cyrilknops/intelliflow/2020-2021/PCB/TestCodesPCB/UART_Master/UART_Master.ino

const char *sending = "Hello from ESP32";
String reading;
  
void setup()
{
  Serial.begin(115200);
}
void loop()
{
  Serial.println(sending);             
 
   while(Serial.available()) 
   {
   reading = Serial.readString();// read the incoming data as string  
   Serial.println(reading);// string is recieved but it will send it back to the psoc4
   }
   
  delay(1000);
}
