cyrilknops/intelliflow/2020-2021/PCB/TestCodesPCB/PSoc_Slave_Codes/SPI_Slave_FullDuplex.cydsn/codegentemp/UART_Putty_BOOT.h

/***************************************************************************//**
* \file UART_Putty_BOOT.h
* \version 4.0
*
* \brief
*  This file provides constants and parameter values of the bootloader
*  communication APIs for the SCB Component.
*
* Note:
*
********************************************************************************
* \copyright
* Copyright 2014-2017, Cypress Semiconductor Corporation. All rights reserved.
* You may use this file only in accordance with the license, terms, conditions,
* disclaimers, and limitations in the end user license agreement accompanying
* the software package with which this file was provided.
*******************************************************************************/

#if !defined(CY_SCB_BOOT_UART_Putty_H)
#define CY_SCB_BOOT_UART_Putty_H

#include "UART_Putty_PVT.h"

#if (UART_Putty_SCB_MODE_I2C_INC)
    #include "UART_Putty_I2C.h"
#endif /* (UART_Putty_SCB_MODE_I2C_INC) */

#if (UART_Putty_SCB_MODE_EZI2C_INC)
    #include "UART_Putty_EZI2C.h"
#endif /* (UART_Putty_SCB_MODE_EZI2C_INC) */

#if (UART_Putty_SCB_MODE_SPI_INC || UART_Putty_SCB_MODE_UART_INC)
    #include "UART_Putty_SPI_UART.h"
#endif /* (UART_Putty_SCB_MODE_SPI_INC || UART_Putty_SCB_MODE_UART_INC) */


/***************************************
*  Conditional Compilation Parameters
****************************************/

/* Bootloader communication interface enable */
#define UART_Putty_BTLDR_COMM_ENABLED ((CYDEV_BOOTLOADER_IO_COMP == CyBtldr_UART_Putty) || \
                                             (CYDEV_BOOTLOADER_IO_COMP == CyBtldr_Custom_Interface))

/* Enable I2C bootloader communication */
#if (UART_Putty_SCB_MODE_I2C_INC)
    #define UART_Putty_I2C_BTLDR_COMM_ENABLED     (UART_Putty_BTLDR_COMM_ENABLED && \
                                                            (UART_Putty_SCB_MODE_UNCONFIG_CONST_CFG || \
                                                             UART_Putty_I2C_SLAVE_CONST))
#else
     #define UART_Putty_I2C_BTLDR_COMM_ENABLED    (0u)
#endif /* (UART_Putty_SCB_MODE_I2C_INC) */

/* EZI2C does not support bootloader communication. Provide empty APIs */
#if (UART_Putty_SCB_MODE_EZI2C_INC)
    #define UART_Putty_EZI2C_BTLDR_COMM_ENABLED   (UART_Putty_BTLDR_COMM_ENABLED && \
                                                         UART_Putty_SCB_MODE_UNCONFIG_CONST_CFG)
#else
    #define UART_Putty_EZI2C_BTLDR_COMM_ENABLED   (0u)
#endif /* (UART_Putty_EZI2C_BTLDR_COMM_ENABLED) */

/* Enable SPI bootloader communication */
#if (UART_Putty_SCB_MODE_SPI_INC)
    #define UART_Putty_SPI_BTLDR_COMM_ENABLED     (UART_Putty_BTLDR_COMM_ENABLED && \
                                                            (UART_Putty_SCB_MODE_UNCONFIG_CONST_CFG || \
                                                             UART_Putty_SPI_SLAVE_CONST))
#else
        #define UART_Putty_SPI_BTLDR_COMM_ENABLED (0u)
#endif /* (UART_Putty_SPI_BTLDR_COMM_ENABLED) */

/* Enable UART bootloader communication */
#if (UART_Putty_SCB_MODE_UART_INC)
       #define UART_Putty_UART_BTLDR_COMM_ENABLED    (UART_Putty_BTLDR_COMM_ENABLED && \
                                                            (UART_Putty_SCB_MODE_UNCONFIG_CONST_CFG || \
                                                             (UART_Putty_UART_RX_DIRECTION && \
                                                              UART_Putty_UART_TX_DIRECTION)))
#else
     #define UART_Putty_UART_BTLDR_COMM_ENABLED   (0u)
#endif /* (UART_Putty_UART_BTLDR_COMM_ENABLED) */

/* Enable bootloader communication */
#define UART_Putty_BTLDR_COMM_MODE_ENABLED    (UART_Putty_I2C_BTLDR_COMM_ENABLED   || \
                                                     UART_Putty_SPI_BTLDR_COMM_ENABLED   || \
                                                     UART_Putty_EZI2C_BTLDR_COMM_ENABLED || \
                                                     UART_Putty_UART_BTLDR_COMM_ENABLED)


/***************************************
*        Function Prototypes
***************************************/

#if defined(CYDEV_BOOTLOADER_IO_COMP) && (UART_Putty_I2C_BTLDR_COMM_ENABLED)
    /* I2C Bootloader physical layer functions */
    void UART_Putty_I2CCyBtldrCommStart(void);
    void UART_Putty_I2CCyBtldrCommStop (void);
    void UART_Putty_I2CCyBtldrCommReset(void);
    cystatus UART_Putty_I2CCyBtldrCommRead       (uint8 pData[], uint16 size, uint16 * count, uint8 timeOut);
    cystatus UART_Putty_I2CCyBtldrCommWrite(const uint8 pData[], uint16 size, uint16 * count, uint8 timeOut);

    /* Map I2C specific bootloader communication APIs to SCB specific APIs */
    #if (UART_Putty_SCB_MODE_I2C_CONST_CFG)
        #define UART_Putty_CyBtldrCommStart   UART_Putty_I2CCyBtldrCommStart
        #define UART_Putty_CyBtldrCommStop    UART_Putty_I2CCyBtldrCommStop
        #define UART_Putty_CyBtldrCommReset   UART_Putty_I2CCyBtldrCommReset
        #define UART_Putty_CyBtldrCommRead    UART_Putty_I2CCyBtldrCommRead
        #define UART_Putty_CyBtldrCommWrite   UART_Putty_I2CCyBtldrCommWrite
    #endif /* (UART_Putty_SCB_MODE_I2C_CONST_CFG) */

#endif /* defined(CYDEV_BOOTLOADER_IO_COMP) && (UART_Putty_I2C_BTLDR_COMM_ENABLED) */


#if defined(CYDEV_BOOTLOADER_IO_COMP) && (UART_Putty_EZI2C_BTLDR_COMM_ENABLED)
    /* Bootloader physical layer functions */
    void UART_Putty_EzI2CCyBtldrCommStart(void);
    void UART_Putty_EzI2CCyBtldrCommStop (void);
    void UART_Putty_EzI2CCyBtldrCommReset(void);
    cystatus UART_Putty_EzI2CCyBtldrCommRead       (uint8 pData[], uint16 size, uint16 * count, uint8 timeOut);
    cystatus UART_Putty_EzI2CCyBtldrCommWrite(const uint8 pData[], uint16 size, uint16 * count, uint8 timeOut);

    /* Map EZI2C specific bootloader communication APIs to SCB specific APIs */
    #if (UART_Putty_SCB_MODE_EZI2C_CONST_CFG)
        #define UART_Putty_CyBtldrCommStart   UART_Putty_EzI2CCyBtldrCommStart
        #define UART_Putty_CyBtldrCommStop    UART_Putty_EzI2CCyBtldrCommStop
        #define UART_Putty_CyBtldrCommReset   UART_Putty_EzI2CCyBtldrCommReset
        #define UART_Putty_CyBtldrCommRead    UART_Putty_EzI2CCyBtldrCommRead
        #define UART_Putty_CyBtldrCommWrite   UART_Putty_EzI2CCyBtldrCommWrite
    #endif /* (UART_Putty_SCB_MODE_EZI2C_CONST_CFG) */

#endif /* defined(CYDEV_BOOTLOADER_IO_COMP) && (UART_Putty_EZI2C_BTLDR_COMM_ENABLED) */

#if defined(CYDEV_BOOTLOADER_IO_COMP) && (UART_Putty_SPI_BTLDR_COMM_ENABLED)
    /* SPI Bootloader physical layer functions */
    void UART_Putty_SpiCyBtldrCommStart(void);
    void UART_Putty_SpiCyBtldrCommStop (void);
    void UART_Putty_SpiCyBtldrCommReset(void);
    cystatus UART_Putty_SpiCyBtldrCommRead       (uint8 pData[], uint16 size, uint16 * count, uint8 timeOut);
    cystatus UART_Putty_SpiCyBtldrCommWrite(const uint8 pData[], uint16 size, uint16 * count, uint8 timeOut);

    /* Map SPI specific bootloader communication APIs to SCB specific APIs */
    #if (UART_Putty_SCB_MODE_SPI_CONST_CFG)
        #define UART_Putty_CyBtldrCommStart   UART_Putty_SpiCyBtldrCommStart
        #define UART_Putty_CyBtldrCommStop    UART_Putty_SpiCyBtldrCommStop
        #define UART_Putty_CyBtldrCommReset   UART_Putty_SpiCyBtldrCommReset
        #define UART_Putty_CyBtldrCommRead    UART_Putty_SpiCyBtldrCommRead
        #define UART_Putty_CyBtldrCommWrite   UART_Putty_SpiCyBtldrCommWrite
    #endif /* (UART_Putty_SCB_MODE_SPI_CONST_CFG) */

#endif /* defined(CYDEV_BOOTLOADER_IO_COMP) && (UART_Putty_SPI_BTLDR_COMM_ENABLED) */

#if defined(CYDEV_BOOTLOADER_IO_COMP) && (UART_Putty_UART_BTLDR_COMM_ENABLED)
    /* UART Bootloader physical layer functions */
    void UART_Putty_UartCyBtldrCommStart(void);
    void UART_Putty_UartCyBtldrCommStop (void);
    void UART_Putty_UartCyBtldrCommReset(void);
    cystatus UART_Putty_UartCyBtldrCommRead       (uint8 pData[], uint16 size, uint16 * count, uint8 timeOut);
    cystatus UART_Putty_UartCyBtldrCommWrite(const uint8 pData[], uint16 size, uint16 * count, uint8 timeOut);

    /* Map UART specific bootloader communication APIs to SCB specific APIs */
    #if (UART_Putty_SCB_MODE_UART_CONST_CFG)
        #define UART_Putty_CyBtldrCommStart   UART_Putty_UartCyBtldrCommStart
        #define UART_Putty_CyBtldrCommStop    UART_Putty_UartCyBtldrCommStop
        #define UART_Putty_CyBtldrCommReset   UART_Putty_UartCyBtldrCommReset
        #define UART_Putty_CyBtldrCommRead    UART_Putty_UartCyBtldrCommRead
        #define UART_Putty_CyBtldrCommWrite   UART_Putty_UartCyBtldrCommWrite
    #endif /* (UART_Putty_SCB_MODE_UART_CONST_CFG) */

#endif /* defined(CYDEV_BOOTLOADER_IO_COMP) && (UART_Putty_UART_BTLDR_COMM_ENABLED) */

/**
* \addtogroup group_bootloader
* @{
*/

#if defined(CYDEV_BOOTLOADER_IO_COMP) && (UART_Putty_BTLDR_COMM_ENABLED)
    #if (UART_Putty_SCB_MODE_UNCONFIG_CONST_CFG)
        /* Bootloader physical layer functions */
        void UART_Putty_CyBtldrCommStart(void);
        void UART_Putty_CyBtldrCommStop (void);
        void UART_Putty_CyBtldrCommReset(void);
        cystatus UART_Putty_CyBtldrCommRead       (uint8 pData[], uint16 size, uint16 * count, uint8 timeOut);
        cystatus UART_Putty_CyBtldrCommWrite(const uint8 pData[], uint16 size, uint16 * count, uint8 timeOut);
    #endif /* (UART_Putty_SCB_MODE_UNCONFIG_CONST_CFG) */

    /* Map SCB specific bootloader communication APIs to common APIs */
    #if (CYDEV_BOOTLOADER_IO_COMP == CyBtldr_UART_Putty)
        #define CyBtldrCommStart    UART_Putty_CyBtldrCommStart
        #define CyBtldrCommStop     UART_Putty_CyBtldrCommStop
        #define CyBtldrCommReset    UART_Putty_CyBtldrCommReset
        #define CyBtldrCommWrite    UART_Putty_CyBtldrCommWrite
        #define CyBtldrCommRead     UART_Putty_CyBtldrCommRead
    #endif /* (CYDEV_BOOTLOADER_IO_COMP == CyBtldr_UART_Putty) */

#endif /* defined(CYDEV_BOOTLOADER_IO_COMP) && (UART_Putty_BTLDR_COMM_ENABLED) */

/** @} group_bootloader */

/***************************************
*           API Constants
***************************************/

/* Timeout unit in milliseconds */
#define UART_Putty_WAIT_1_MS  (1u)

/* Return number of bytes to copy into bootloader buffer */
#define UART_Putty_BYTES_TO_COPY(actBufSize, bufSize) \
                            ( ((uint32)(actBufSize) < (uint32)(bufSize)) ? \
                                ((uint32) (actBufSize)) : ((uint32) (bufSize)) )

/* Size of Read/Write buffers for I2C bootloader  */
#define UART_Putty_I2C_BTLDR_SIZEOF_READ_BUFFER   (64u)
#define UART_Putty_I2C_BTLDR_SIZEOF_WRITE_BUFFER  (64u)

/* Byte to byte time interval: calculated basing on current component
* data rate configuration, can be defined in project if required.
*/
#ifndef UART_Putty_SPI_BYTE_TO_BYTE
    #define UART_Putty_SPI_BYTE_TO_BYTE   (160u)
#endif

/* Byte to byte time interval: calculated basing on current component
* baud rate configuration, can be defined in the project if required.
*/
#ifndef UART_Putty_UART_BYTE_TO_BYTE
    #define UART_Putty_UART_BYTE_TO_BYTE  (2086u)
#endif /* UART_Putty_UART_BYTE_TO_BYTE */

#endif /* (CY_SCB_BOOT_UART_Putty_H) */


/* [] END OF FILE */
