cyrilknops/intelliflow/2020-2021/PCB/TestCodesPCB/PSoc_Slave_Codes/I2C_slave.cydsn/codegentemp/EZI2C_EZI2C_INT.c

/***************************************************************************//**
* \file EZI2C_EZI2C_INT.c
* \version 4.0
*
* \brief
*  This file provides the source code to the Interrupt Service Routine for
*  the SCB Component in EZI2C mode.
*
* Note:
*
********************************************************************************
* \copyright
* Copyright 2013-2017, Cypress Semiconductor Corporation.  All rights reserved.
* You may use this file only in accordance with the license, terms, conditions,
* disclaimers, and limitations in the end user license agreement accompanying
* the software package with which this file was provided.
*******************************************************************************/

#include "EZI2C_PVT.h"
#include "EZI2C_EZI2C_PVT.h"
#include "cyapicallbacks.h"

#if(EZI2C_EZI2C_SCL_STRETCH_ENABLE_CONST)
    /*******************************************************************************
    * Function Name: EZI2C_EZI2C_STRETCH_ISR
    ****************************************************************************//**
    *
    *  Handles the Interrupt Service Routine for the SCB EZI2C mode.
    *  The clock stretching is used during operation.
    *
    *******************************************************************************/
    CY_ISR_PROTO(EZI2C_EZI2C_STRETCH_ISR)
    {
        static uint16 locBufSize;
        uint32 locIndex;
        uint32 locStatus;

        uint32 endTransfer;
        uint32 fifoIndex;
        uint32 locByte;

        uint32 locIntrCause;
        uint32 locIntrSlave;

    #ifdef EZI2C_EZI2C_STRETCH_ISR_ENTRY_CALLBACK
        EZI2C_EZI2C_STRETCH_ISR_EntryCallback();
    #endif /* EZI2C_EZI2C_STRETCH_ISR_ENTRY_CALLBACK */

    #if(EZI2C_SECONDARY_ADDRESS_ENABLE_CONST)
        /* Variable intended to be used with either buffer */
        static volatile uint8 * EZI2C_dataBuffer; /* Pointer to data buffer              */
        static uint16 EZI2C_bufSizeBuf;           /* Size of buffer in bytes             */
        static uint16 EZI2C_protectBuf;           /* Start index of write protected area */

        static uint8 activeAddress;
        uint32 ackResponse;

        ackResponse = EZI2C_EZI2C_ACK_RECEIVED_ADDRESS;
    #endif /* (EZI2C_SECONDARY_ADDRESS_ENABLE_CONST) */

    #if !defined (CY_REMOVE_EZI2C_CUSTOM_INTR_HANDLER)
        if(NULL != EZI2C_customIntrHandler)
        {
            EZI2C_customIntrHandler();
        }
    #else
        CY_EZI2C_CUSTOM_INTR_HANDLER();
    #endif /* !defined (CY_REMOVE_EZI2C_CUSTOM_INTR_HANDLER) */

        /* Make local copy of global variable */
        locIndex = EZI2C_EZI2C_GET_INDEX(activeAddress);

        /* Get interrupt sources */
        locIntrSlave = EZI2C_GetSlaveInterruptSource();
        locIntrCause = EZI2C_GetInterruptCause();

        /* INTR_SLAVE.I2C_ARB_LOST and INTR_SLAVE_I2C.BUS_ERROR */
        /* Handles errors on the bus. There are cases when both bits are set.
        * The error recovery is common: re-enable the scb IP. The content of the RX FIFO is lost.
        */
        if(0u != (locIntrSlave & (EZI2C_INTR_SLAVE_I2C_ARB_LOST |
                                  EZI2C_INTR_SLAVE_I2C_BUS_ERROR)))
        {
            EZI2C_CTRL_REG &= (uint32) ~EZI2C_CTRL_ENABLED; /* Disable SCB block */

        #if(EZI2C_CY_SCBIP_V0)
            if(0u != ((uint8) EZI2C_EZI2C_STATUS_BUSY & EZI2C_curStatus))
        #endif /* (EZI2C_CY_SCBIP_V0) */
            {
                EZI2C_curStatus &= (uint8) ~EZI2C_EZI2C_STATUS_BUSY;
                EZI2C_curStatus |= (uint8)  EZI2C_EZI2C_STATUS_ERR;

                /* INTR_TX_EMPTY is enabled in the address phase to receive data */
                if(0u == (EZI2C_GetTxInterruptMode() & EZI2C_INTR_TX_EMPTY))
                {
                    /* Write complete */
                    if(EZI2C_indexBuf1 != EZI2C_offsetBuf1)
                    {
                        EZI2C_curStatus |= (uint8) EZI2C_INTR_SLAVE_I2C_WRITE_STOP;
                    }
                }
                else
                {
                    /* Read complete */
                    EZI2C_curStatus |= (uint8) EZI2C_INTR_SLAVE_I2C_NACK;
                }
            }

            EZI2C_DISABLE_SLAVE_AUTO_DATA;

            /* Disable TX and RX interrupt sources */
            EZI2C_SetRxInterruptMode(EZI2C_NO_INTR_SOURCES);
            EZI2C_SetTxInterruptMode(EZI2C_NO_INTR_SOURCES);

        #if(EZI2C_CY_SCBIP_V0)
            /* Clear interrupt sources as they are not automatically cleared after SCB is disabled */
            EZI2C_ClearRxInterruptSource(EZI2C_INTR_RX_ALL);
            EZI2C_ClearSlaveInterruptSource(EZI2C_INTR_SLAVE_ALL);
        #endif /* (EZI2C_CY_SCBIP_V0) */

            EZI2C_fsmState = EZI2C_EZI2C_FSM_IDLE;

            EZI2C_CTRL_REG |= (uint32) EZI2C_CTRL_ENABLED;  /* Enable SCB block */
        }
        else
        {
            /* INTR_I2C_EC_WAKE_UP */
            /* Wakes up device from deep sleep */
            if(0u != (locIntrCause & EZI2C_INTR_CAUSE_I2C_EC))
            {
                /* Disables wakeup interrupt source but does not clear it. It is cleared in INTR_SLAVE_I2C_ADDR_MATCH */
                EZI2C_SetI2CExtClkInterruptMode(EZI2C_NO_INTR_SOURCES);
            }

            if(0u != (locIntrCause & (EZI2C_INTR_CAUSE_RX | EZI2C_INTR_CAUSE_SLAVE)))
            {
                /* INTR_RX.NOT_EMPTY */
                /* Receives data byte-by-byte. Does not use RX FIFO capabilities */
                if (0u != (EZI2C_GetRxInterruptSourceMasked() & EZI2C_INTR_RX_NOT_EMPTY))
                {
                #if(EZI2C_SECONDARY_ADDRESS_ENABLE_CONST)
                    /* If I2C_STOP service is delayed to I2C_ADDR_MATCH the address byte is in the RX FIFO and
                    * RX_NOT_EMPTY is enabled. The address byte has to stay into RX FIFO therefore
                    * RX.NOT_EMPTY service has to be skipped. The address byte has to be read by I2C_ADDR_MATCH.
                    */
                    if (0u == (locIntrCause & EZI2C_INTR_CAUSE_SLAVE))
                #endif /* (EZI2C_SECONDARY_ADDRESS_ENABLE_CONST) */
                    {
                        locByte = EZI2C_RX_FIFO_RD_REG;

                        switch(EZI2C_fsmState)
                        {
                        case EZI2C_EZI2C_FSM_BYTE_WRITE:
                            if(0u != locBufSize)
                            {
                                /* Store data byte and ACK */
                                EZI2C_I2C_SLAVE_GENERATE_ACK;

                                EZI2C_dataBuffer1[locIndex] = (uint8) locByte;
                                locIndex++;
                                locBufSize--;
                            }
                            else
                            {
                                /* Discard data byte and NACK */
                                EZI2C_I2C_SLAVE_GENERATE_NACK;
                            }
                            break;

                    #if(EZI2C_SUB_ADDRESS_SIZE16_CONST)
                        case EZI2C_EZI2C_FSM_OFFSET_HI8:

                            EZI2C_I2C_SLAVE_GENERATE_ACK;

                            /* Store offset most significant byre */
                            locBufSize = (uint16) ((uint8) locByte);

                            EZI2C_fsmState = EZI2C_EZI2C_FSM_OFFSET_LO8;

                            break;
                    #endif /* (EZI2C_SUB_ADDRESS_SIZE16_CONST) */

                        case EZI2C_EZI2C_FSM_OFFSET_LO8:

                            #if (EZI2C_SUB_ADDRESS_SIZE16)
                            {
                                /* Collect 2 bytes offset */
                                locByte = ((uint32) ((uint32) locBufSize << 8u)) | locByte;
                            }
                            #endif

                            /* Check offset against buffer size */
                            if(locByte < (uint32) EZI2C_bufSizeBuf1)
                            {
                                EZI2C_I2C_SLAVE_GENERATE_ACK;

                                /* Update local buffer index with new offset */
                                locIndex = locByte;

                                /* Get available buffer size to write */
                                locBufSize = (uint16) ((locByte < EZI2C_protectBuf1) ?
                                                       (EZI2C_protectBuf1 - locByte) : (0u));

                            #if(EZI2C_CY_SCBIP_V0)

                                if(locBufSize < EZI2C_EZI2C_FIFO_SIZE)
                                {
                                    /* Set FSM state to receive byte by byte */
                                    EZI2C_fsmState = EZI2C_EZI2C_FSM_BYTE_WRITE;
                                }
                                /* Receive RX FIFO chunks */
                                else if(locBufSize == EZI2C_EZI2C_FIFO_SIZE)
                                {
                                    EZI2C_ENABLE_SLAVE_AUTO_DATA; /* NACK when RX FIFO is full */
                                    EZI2C_SetRxInterruptMode(EZI2C_NO_INTR_SOURCES);
                                }
                                else
                                {
                                    EZI2C_ENABLE_SLAVE_AUTO_DATA_ACK; /* Stretch when RX FIFO is full */
                                    EZI2C_SetRxInterruptMode(EZI2C_INTR_RX_FULL);
                                }

                            #else

                                #if(EZI2C_SECONDARY_ADDRESS_ENABLE)
                                {
                                    /* Set FSM state to receive byte by byte.
                                    * The byte by byte receive is always chosen for two addresses. Ticket ID#175559.
                                    */
                                    EZI2C_fsmState = EZI2C_EZI2C_FSM_BYTE_WRITE;
                                }
                                #else
                                {
                                    if (locBufSize < EZI2C_EZI2C_FIFO_SIZE)
                                    {
                                        /* Set FSM state to receive byte by byte */
                                        EZI2C_fsmState = EZI2C_EZI2C_FSM_BYTE_WRITE;
                                    }
                                    /* Receive RX FIFO chunks */
                                    else if (locBufSize == EZI2C_EZI2C_FIFO_SIZE)
                                    {
                                        EZI2C_ENABLE_SLAVE_AUTO_DATA; /* NACK when RX FIFO is full */
                                        EZI2C_SetRxInterruptMode(EZI2C_NO_INTR_SOURCES);
                                    }
                                    else
                                    {
                                        EZI2C_ENABLE_SLAVE_AUTO_DATA_ACK; /* Stretch when RX FIFO is full */
                                        EZI2C_SetRxInterruptMode(EZI2C_INTR_RX_FULL);
                                    }
                                }
                                #endif

                            #endif /* (EZI2C_CY_SCBIP_V0) */

                                /* Store local offset into global variable */
                                EZI2C_EZI2C_SET_OFFSET(activeAddress, locIndex);
                            }
                            else
                            {
                                /* Discard offset byte and NACK */
                                EZI2C_I2C_SLAVE_GENERATE_NACK;
                            }
                            break;

                        default:
                            CYASSERT(0u != 0u); /* Should never get there */
                            break;
                        }

                        EZI2C_ClearRxInterruptSource(EZI2C_INTR_RX_NOT_EMPTY);
                    }
                }
                /* INTR_RX.FULL, INTR_SLAVE.I2C_STOP */
                /* Receive FIFO chunks: auto data ACK is enabled */
                else if (0u != (EZI2C_I2C_CTRL_REG & EZI2C_I2C_CTRL_S_READY_DATA_ACK))
                {
                    /* Slave interrupt (I2C_STOP or I2C_ADDR_MATCH) leads to completion of read.
                    * A completion event has a higher priority than the FIFO full.
                    * Read remaining data from RX FIFO.
                    */
                    if(0u != (locIntrCause & EZI2C_INTR_CAUSE_SLAVE))
                    {
                        /* Read remaining bytes from RX FIFO */
                        fifoIndex = EZI2C_GET_RX_FIFO_ENTRIES;

                        #if(EZI2C_SECONDARY_ADDRESS_ENABLE)
                        {
                            /* Update with current address match */
                            if(EZI2C_CHECK_INTR_SLAVE_MASKED(EZI2C_INTR_SLAVE_I2C_ADDR_MATCH))
                            {
                                /* Update RX FIFO entries as address byte is there now */
                                fifoIndex = EZI2C_GET_RX_FIFO_ENTRIES;

                                /* If SR is valid, RX FIFO is full and address is in SHIFTER:
                                * read 8 entries and leave address in RX FIFO for further processing.
                                * If SR is invalid, address is already in RX FIFO: read (entries-1).
                                */
                                fifoIndex -= ((0u != EZI2C_GET_RX_FIFO_SR_VALID) ? (0u) : (1u));
                            }
                        }
                        #endif

                        EZI2C_DISABLE_SLAVE_AUTO_DATA;
                        endTransfer = EZI2C_EZI2C_CONTINUE_TRANSFER;
                    }
                    else
                    /* INTR_RX_FULL */
                    /* Continue transfer or disable INTR_RX_FULL to catch completion event. */
                    {
                        /* Calculate buffer size available to write data into */
                        locBufSize -= (uint16) EZI2C_EZI2C_FIFO_SIZE;

                        if(locBufSize <= EZI2C_EZI2C_FIFO_SIZE)
                        {
                            /* Send NACK when RX FIFO overflow */
                            fifoIndex   = locBufSize;
                            endTransfer = EZI2C_EZI2C_COMPLETE_TRANSFER;
                        }
                        else
                        {
                            /* Continue  transaction */
                            fifoIndex   = EZI2C_EZI2C_FIFO_SIZE;
                            endTransfer = EZI2C_EZI2C_CONTINUE_TRANSFER;
                        }
                    }

                    for(; (0u != fifoIndex); fifoIndex--)
                    {
                        /* Store data in buffer */
                        EZI2C_dataBuffer1[locIndex] = (uint8) EZI2C_RX_FIFO_RD_REG;
                        locIndex++;
                    }

                    /* Complete transfer sending NACK when RX FIFO overflow */
                    if(EZI2C_EZI2C_COMPLETE_TRANSFER == endTransfer)
                    {
                        EZI2C_ENABLE_SLAVE_AUTO_DATA_NACK;

                        /* Disable INTR_RX_FULL during last RX FIFO chunk reception */
                        EZI2C_SetRxInterruptMode(EZI2C_NO_INTR_SOURCES);
                    }

                    EZI2C_ClearRxInterruptSource(EZI2C_INTR_RX_FULL |
                                                            EZI2C_INTR_RX_NOT_EMPTY);
                }
                else
                {
                    /* Exit for slave interrupts which are not active for RX direction:
                    * INTR_SLAVE.I2C_ADDR_MATCH and INTR_SLAVE.I2C_STOP while byte-by-byte reception.
                    */
                }
            }

            if(0u != (locIntrCause & EZI2C_INTR_CAUSE_SLAVE))
            {
                /* INTR_SLAVE.I2C_STOP */
                /* Catch Stop condition: completion of write or read transfer */
            #if(!EZI2C_SECONDARY_ADDRESS_ENABLE_CONST)
                if(0u != (locIntrSlave & EZI2C_INTR_SLAVE_I2C_STOP))
            #else
                /* Prevent triggering when matched address was NACKed */
                if((0u != (locIntrSlave & EZI2C_INTR_SLAVE_I2C_STOP)) &&
                   (0u != ((uint8) EZI2C_EZI2C_STATUS_BUSY & EZI2C_curStatus)))
            #endif
                {
                    /* Disable TX and RX interrupt sources */
                    EZI2C_SetRxInterruptMode(EZI2C_NO_INTR_SOURCES);
                    EZI2C_SetTxInterruptMode(EZI2C_NO_INTR_SOURCES);

                    /* Set read completion mask */
                    locStatus = EZI2C_INTR_SLAVE_I2C_NACK;

                    /* Check if buffer content was modified: the address phase resets the locIndex */
                    if(locIndex != EZI2C_EZI2C_GET_OFFSET(activeAddress))
                    {
                        locStatus |= EZI2C_INTR_SLAVE_I2C_WRITE_STOP;
                    }

                    /* Complete read or write transaction */
                    locStatus &= locIntrSlave;
                    EZI2C_EZI2C_UPDATE_LOC_STATUS(activeAddress, locStatus);
                    locStatus |= (uint32)  EZI2C_curStatus;
                    locStatus &= (uint32) ~EZI2C_EZI2C_STATUS_BUSY;
                    EZI2C_curStatus = (uint8) locStatus;

                    EZI2C_fsmState = EZI2C_EZI2C_FSM_IDLE;

                    #if(EZI2C_SECONDARY_ADDRESS_ENABLE)
                    {
                        /* Store local index into global variable, before address phase */
                        EZI2C_EZI2C_SET_INDEX(activeAddress, locIndex);
                    }
                    #endif
                }

                /* INTR_SLAVE.I2C_ADDR_MATCH */
                /* The matched address is received: the slave starts its operation.
                * INTR_SLAVE_I2C_STOP updates the buffer index before the address phase for two addresses mode.
                * This is done to update buffer index correctly before the address phase changes it.
                */
                if(0u != (locIntrSlave & EZI2C_INTR_SLAVE_I2C_ADDR_MATCH))
                {
                    #if(EZI2C_SECONDARY_ADDRESS_ENABLE)
                    {
                        /* Read address byte from RX FIFO */
                        locByte = EZI2C_GET_I2C_7BIT_ADDRESS(EZI2C_RX_FIFO_RD_REG);

                        EZI2C_ClearRxInterruptSource(EZI2C_INTR_RX_NOT_EMPTY);

                        /* Check received address against device addresses */
                        if(EZI2C_addrBuf1 == locByte)
                        {
                            /* Set buffer exposed to primary slave address */
                            EZI2C_dataBuffer = EZI2C_dataBuffer1;
                            EZI2C_bufSizeBuf = EZI2C_bufSizeBuf1;
                            EZI2C_protectBuf = EZI2C_protectBuf1;

                            activeAddress = EZI2C_EZI2C_ACTIVE_ADDRESS1;
                        }
                        else if(EZI2C_addrBuf2 == locByte)
                        {
                            /* Set buffer exposed to secondary slave address */
                            EZI2C_dataBuffer = EZI2C_dataBuffer2;
                            EZI2C_bufSizeBuf = EZI2C_bufSizeBuf2;
                            EZI2C_protectBuf = EZI2C_protectBuf2;

                            activeAddress = EZI2C_EZI2C_ACTIVE_ADDRESS2;
                        }
                        else
                        {
                            /* Address does not match */
                            ackResponse = EZI2C_EZI2C_NACK_RECEIVED_ADDRESS;
                        }
                    }
                    #endif

                #if(EZI2C_SECONDARY_ADDRESS_ENABLE_CONST)
                    if(EZI2C_EZI2C_NACK_RECEIVED_ADDRESS == ackResponse)
                    {
                        /* Clear interrupt sources before NACK address */
                        EZI2C_ClearI2CExtClkInterruptSource(EZI2C_INTR_I2C_EC_WAKE_UP);
                        EZI2C_ClearSlaveInterruptSource(EZI2C_INTR_SLAVE_ALL);

                    #if(!EZI2C_CY_SCBIP_V0)
                        /* Disable INTR_I2C_STOP to not trigger after matched address is NACKed. Ticket ID#156094 */
                        EZI2C_DISABLE_INTR_SLAVE(EZI2C_INTR_SLAVE_I2C_STOP);
                    #endif /* (!EZI2C_CY_SCBIP_V0) */

                        /* NACK address byte: it does not match neither primary nor secondary */
                        EZI2C_I2C_SLAVE_GENERATE_NACK;
                    }
                    else
                #endif /* (EZI2C_SECONDARY_ADDRESS_ENABLE_CONST) */
                    {

                    #if(EZI2C_SCB_MODE_UNCONFIG_CONST_CFG)
                        if(!EZI2C_SECONDARY_ADDRESS_ENABLE)
                        {
                            /* Set buffer exposed to primary slave address */
                            EZI2C_dataBuffer = EZI2C_dataBuffer1;
                            EZI2C_bufSizeBuf = EZI2C_bufSizeBuf1;
                            EZI2C_protectBuf = EZI2C_protectBuf1;

                            activeAddress = EZI2C_EZI2C_ACTIVE_ADDRESS1;
                        }
                    #endif /* (EZI2C_SCB_MODE_UNCONFIG_CONST_CFG) */

                        /* Bus becomes busy after address is received */
                        EZI2C_curStatus |= (uint8) EZI2C_EZI2C_STATUS_BUSY;

                        /* Slave is read or written: set current offset */
                        locIndex = EZI2C_EZI2C_GET_OFFSET(activeAddress);

                        /* Check transaction direction */
                        if(EZI2C_CHECK_I2C_STATUS(EZI2C_I2C_STATUS_S_READ))
                        {
                            /* Calculate slave buffer size */
                            locBufSize = EZI2C_bufSizeBuf1 - (uint16) locIndex;

                            /* Clear TX FIFO to start fill from offset */
                            EZI2C_CLEAR_TX_FIFO;
                            EZI2C_SetTxInterruptMode(EZI2C_INTR_TX_EMPTY);
                        }
                        else
                        {
                            /* Master writes: enable reception interrupt. The FSM state was set in INTR_SLAVE_I2C_STOP */
                            EZI2C_SetRxInterruptMode(EZI2C_INTR_RX_NOT_EMPTY);
                        }

                        /* Clear interrupt sources before ACK address */
                        EZI2C_ClearI2CExtClkInterruptSource(EZI2C_INTR_I2C_EC_WAKE_UP);
                        EZI2C_ClearSlaveInterruptSource(EZI2C_INTR_SLAVE_ALL);

                    #if (!EZI2C_CY_SCBIP_V0)
                        /* Enable STOP to trigger after address match is ACKed. Ticket ID#156094 */
                        EZI2C_ENABLE_INTR_SLAVE(EZI2C_INTR_SLAVE_I2C_STOP);
                    #endif /* (!EZI2C_CY_SCBIP_V0) */

                        /* ACK the address byte */
                        EZI2C_I2C_SLAVE_GENERATE_ACK;
                    }
                }

                /* Clear slave interrupt sources */
                EZI2C_ClearSlaveInterruptSource(locIntrSlave);
            }

            /* INTR_TX.EMPTY */
            /* Transmits data to the master: loads data into the TX FIFO. The 0xFF sends out if the master reads
            * out the buffer. The address reception with a read flag clears the TX FIFO to be loaded with data.
            */
            if(0u != (EZI2C_GetInterruptCause() & EZI2C_INTR_CAUSE_TX))
            {
                /* Put data into TX FIFO until there is a room */
                do
                {
                    /* Check transmit buffer range: locBufSize calculates after address reception */
                    if(0u != locBufSize)
                    {
                        EZI2C_TX_FIFO_WR_REG = (uint32) EZI2C_dataBuffer1[locIndex];
                        locIndex++;
                        locBufSize--;
                    }
                    else
                    {
                        EZI2C_TX_FIFO_WR_REG = EZI2C_EZI2C_OVFL_RETURN;
                    }
                }
                while(EZI2C_EZI2C_FIFO_SIZE != EZI2C_GET_TX_FIFO_ENTRIES);

                EZI2C_ClearTxInterruptSource(EZI2C_INTR_TX_EMPTY);
            }
        }

        /* Store local index copy into global variable */
        EZI2C_EZI2C_SET_INDEX(activeAddress, locIndex);

    #ifdef EZI2C_EZI2C_STRETCH_ISR_EXIT_CALLBACK
        EZI2C_EZI2C_STRETCH_ISR_ExitCallback();
    #endif /* EZI2C_EZI2C_STRETCH_ISR_EXIT_CALLBACK */

    }
#endif /* (EZI2C_EZI2C_SCL_STRETCH_ENABLE_CONST) */


#if(EZI2C_EZI2C_SCL_STRETCH_DISABLE_CONST)
    /*******************************************************************************
    * Function Name: EZI2C_EZI2C_NO_STRETCH_ISR
    ****************************************************************************//**
    *
    *  Handles the Interrupt Service Routine for the SCB EZI2C mode.
    *  Clock stretching is NOT used during operation.
    *
    *******************************************************************************/
    CY_ISR_PROTO(EZI2C_EZI2C_NO_STRETCH_ISR)
    {
    #if(EZI2C_SUB_ADDRESS_SIZE16_CONST)
        static uint8 locOffset;
    #endif /* (EZI2C_SUB_ADDRESS_SIZE16_CONST) */

        uint32 locByte;
        uint32 locStatus;
        uint32 locIntrSlave;
        uint32 locIntrCause;

    #ifdef EZI2C_EZI2C_NO_STRETCH_ISR_ENTRY_CALLBACK
        EZI2C_EZI2C_NO_STRETCH_ISR_EntryCallback();
    #endif /* EZI2C_EZI2C_NO_STRETCH_ISR_ENTRY_CALLBACK */

    #if !defined (CY_REMOVE_EZI2C_CUSTOM_INTR_HANDLER)
        /* Calls registered customer routine to manage interrupt sources */
        if(NULL != EZI2C_customIntrHandler)
        {
            EZI2C_customIntrHandler();
        }
    #else
        CY_EZI2C_CUSTOM_INTR_HANDLER();
    #endif /* !defined (CY_REMOVE_EZI2C_CUSTOM_INTR_HANDLER) */

        locByte = 0u;

        /* Get copy of triggered slave interrupt sources */
        locIntrSlave = EZI2C_GetSlaveInterruptSource();
        locIntrCause = EZI2C_GetInterruptCause();

        /* INTR_SLAVE.I2C_ARB_LOST and INTR_SLAVE.I2C_BUS_ERROR */
        /* Handles errors on the bus: There are cases when both bits are set.
        * The error recovery is common: re-enable the scb IP. The content of the RX FIFO is lost.
        */
        if(0u != (locIntrSlave & (EZI2C_INTR_SLAVE_I2C_ARB_LOST |
                                  EZI2C_INTR_SLAVE_I2C_BUS_ERROR)))
        {
            EZI2C_CTRL_REG &= (uint32) ~EZI2C_CTRL_ENABLED; /* Disable SCB block */

        #if (EZI2C_CY_SCBIP_V0)
            if(0u != (locIntrSlave & EZI2C_INTR_SLAVE_I2C_ADDR_MATCH))
        #endif /* (EZI2C_CY_SCBIP_V0) */
            {
                EZI2C_curStatus |= (uint8) EZI2C_EZI2C_STATUS_ERR;

                if(0u != (EZI2C_EZI2C_FSM_WRITE_MASK & EZI2C_fsmState))
                {
                    /* Write complete */
                    if(EZI2C_indexBuf1 != EZI2C_offsetBuf1)
                    {
                        EZI2C_curStatus |= (uint8) EZI2C_INTR_SLAVE_I2C_WRITE_STOP;
                    }
                }
                else
                {
                    /* Read complete */
                    EZI2C_curStatus |= (uint8) EZI2C_INTR_SLAVE_I2C_NACK;
                }
            }

            /* Clean-up interrupt sources */
            EZI2C_SetTxInterruptMode(EZI2C_NO_INTR_SOURCES);

        #if (EZI2C_CY_SCBIP_V0)
            /* Clear interrupt sources as they are not automatically cleared after SCB is disabled */
            EZI2C_ClearRxInterruptSource(EZI2C_INTR_RX_NOT_EMPTY);
            EZI2C_ClearSlaveInterruptSource(EZI2C_INTR_SLAVE_ALL);
        #endif /* (EZI2C_CY_SCBIP_V0) */

            EZI2C_fsmState = EZI2C_EZI2C_FSM_IDLE;

            EZI2C_CTRL_REG |= (uint32) EZI2C_CTRL_ENABLED;  /* Enable SCB block */
        }
        else
        {
            /* INTR_RX.NOT_EMPTY */
            /* The slave receives data from the master: accepts into the RX FIFO. At least one entry is available to be
            * read. The offset is written first and all the following bytes are data (expected to be put in the buffer).
            * The slave ACKs all bytes, but it discards them if they do not match the write criteria.
            * The slave NACKs the bytes in the case of an RX FIFO overflow.
            */
            if(0u != (locIntrCause & EZI2C_INTR_CAUSE_RX))
            {
                /* Read byte from the RX FIFO */
                locByte = EZI2C_RX_FIFO_RD_REG;

                switch(EZI2C_fsmState)
                {

                case EZI2C_EZI2C_FSM_BYTE_WRITE:
                    /* Check buffer index against protect area */
                    if(EZI2C_indexBuf1 < EZI2C_protectBuf1)
                    {
                        /* Stores received byte into buffer */
                        EZI2C_dataBuffer1[EZI2C_indexBuf1] = (uint8) locByte;
                        EZI2C_indexBuf1++;
                    }
                    else
                    {
                        /* Discard current byte and sets FSM state to discard following bytes */
                        EZI2C_fsmState = EZI2C_EZI2C_FSM_WAIT_STOP;
                    }

                    break;

            #if(EZI2C_SUB_ADDRESS_SIZE16_CONST)
                case EZI2C_EZI2C_FSM_OFFSET_HI8:

                    /* Store high byte of offset */
                    locOffset = (uint8) locByte;

                    EZI2C_fsmState  = EZI2C_EZI2C_FSM_OFFSET_LO8;

                    break;
            #endif /* (EZI2C_SUB_ADDRESS_SIZE16_CONST) */

                case EZI2C_EZI2C_FSM_OFFSET_LO8:

                    #if(EZI2C_SUB_ADDRESS_SIZE16)
                    {
                        /* Append offset with high byte */
                        locByte = ((uint32) ((uint32) locOffset << 8u)) | locByte;
                    }
                    #endif

                    /* Check if offset within buffer range */
                    if(locByte < (uint32) EZI2C_bufSizeBuf1)
                    {
                        /* Store and sets received offset */
                        EZI2C_offsetBuf1 = (uint8) locByte;
                        EZI2C_indexBuf1  = (uint16) locByte;

                        /* Move FSM to data receive state */
                        EZI2C_fsmState = EZI2C_EZI2C_FSM_BYTE_WRITE;
                    }
                    else
                    {
                        /* Reset index due to TX FIFO fill */
                        EZI2C_indexBuf1 = (uint16) EZI2C_offsetBuf1;

                        /* Discard current byte and sets FSM state to default to discard following bytes */
                        EZI2C_fsmState = EZI2C_EZI2C_FSM_WAIT_STOP;
                    }

                    break;

                case EZI2C_EZI2C_FSM_WAIT_STOP:
                    /* Clear RX FIFO to discard all received data */
                    EZI2C_CLEAR_RX_FIFO;

                    break;

                default:
                    CYASSERT(0u != 0u); /* Should never get there */
                    break;
                }

                EZI2C_ClearRxInterruptSource(EZI2C_INTR_RX_NOT_EMPTY);
            }


            /* INTR_SLAVE.I2C_START */
            /* Catches start of transfer to trigger TX FIFO update event */
            if(0u != (locIntrSlave & EZI2C_INTR_SLAVE_I2C_START))
            {
            #if(!EZI2C_CY_SCBIP_V0)
                #if(EZI2C_EZI2C_EC_AM_ENABLE)
                {
                    /* Manage INTR_I2C_EC.WAKE_UP as slave busy status */
                    EZI2C_ClearI2CExtClkInterruptSource(EZI2C_INTR_I2C_EC_WAKE_UP);
                }
                #else
                {
                    /* Manage INTR_SLAVE.I2C_ADDR_MATCH as slave busy status */
                    EZI2C_ClearSlaveInterruptSource(EZI2C_INTR_SLAVE_I2C_ADDR_MATCH);
                }
                #endif
            #else
                /* Manage INTR_SLAVE.I2C_ADDR_MATCH as slave busy status */
                EZI2C_ClearSlaveInterruptSource(EZI2C_INTR_SLAVE_I2C_ADDR_MATCH);
            #endif /* (EZI2C_CY_SCBIP_V0) */

                /* Clear TX FIFO and put a byte */
                EZI2C_FAST_CLEAR_TX_FIFO;
                EZI2C_TX_FIFO_WR_REG = (uint32) EZI2C_dataBuffer1[EZI2C_offsetBuf1];

                /* Store buffer index to be handled by INTR_SLAVE.I2C_STOP */
                locByte = (uint32) EZI2C_indexBuf1;

                /* Update index: one byte is already in the TX FIFO */
                EZI2C_indexBuf1 = (uint16) EZI2C_offsetBuf1 + 1u;

                /* Enable INTR_TX.NOT_FULL to load TX FIFO */
                EZI2C_SetTxInterruptMode(EZI2C_INTR_TX_TRIGGER);

                /* Clear locIntrSlave after INTR.TX_TRIGGER is enabled */
                EZI2C_ClearSlaveInterruptSource(locIntrSlave);

                locIntrCause |= EZI2C_INTR_CAUSE_TX;
            }


            /* INTR_TX.TRIGGER */
            /* Transmits data to the master: loads data into the TX FIFO. The TX FIFO is loaded with data
            *  until used entries are less than EZI2C_TX_LOAD_SIZE. If index reaches end of the
            *  buffer the 0xFF is sent to the end of transfer.
            */
            if(0u != (locIntrCause & EZI2C_INTR_CAUSE_TX))
            {
                /* Put data into TX FIFO until there is room */
                do
                {
                    /* Check transmit buffer range */
                    if(EZI2C_indexBuf1 < EZI2C_bufSizeBuf1)
                    {
                        EZI2C_TX_FIFO_WR_REG = (uint32) EZI2C_dataBuffer1[EZI2C_indexBuf1];
                        EZI2C_indexBuf1++;
                    }
                    else
                    {
                        EZI2C_TX_FIFO_WR_REG = EZI2C_EZI2C_OVFL_RETURN;
                    }

                }
                while(EZI2C_TX_LOAD_SIZE != EZI2C_GET_TX_FIFO_ENTRIES);

                EZI2C_ClearTxInterruptSource(EZI2C_INTR_TX_TRIGGER);
            }


            /* INTR_SLAVE.I2C_STOP */
            /* Catch completion of write or read transfer. */
            if(0u != (locIntrSlave & EZI2C_INTR_SLAVE_I2C_STOP))
            {
                if(0u == (locIntrSlave & EZI2C_INTR_SLAVE_I2C_START))
                {
                #if(!EZI2C_CY_SCBIP_V0)
                    #if(EZI2C_EZI2C_EC_AM_ENABLE)
                    {
                        /* Manage INTR_I2C_EC.WAKE_UP as slave busy status */
                        EZI2C_ClearI2CExtClkInterruptSource(EZI2C_INTR_I2C_EC_WAKE_UP);
                    }
                    #endif
                #endif /* (!EZI2C_CY_SCBIP_V0) */

                    /* Manage INTR_SLAVE.I2C_ADDR_MATCH as slave busy status */
                    EZI2C_ClearSlaveInterruptSource(locIntrSlave);

                    /* Read current buffer index */
                    locByte = (uint32) EZI2C_indexBuf1;
                }

                /* Set read completion mask */
                locStatus = EZI2C_INTR_SLAVE_I2C_NACK;

                if((locByte != EZI2C_offsetBuf1) &&
                   (0u != (EZI2C_EZI2C_FSM_WRITE_MASK & EZI2C_fsmState)))
                {
                    /* Set write completion mask */
                    locStatus |= EZI2C_INTR_SLAVE_I2C_WRITE_STOP;
                }

                /* Set completion flags in the status variable */
                EZI2C_curStatus |= (uint8) (locStatus & locIntrSlave);

                EZI2C_fsmState = EZI2C_EZI2C_FSM_IDLE;
            }


        #if(!EZI2C_CY_SCBIP_V0)
            #if(EZI2C_EZI2C_EC_AM_ENABLE)
            {
                /* INTR_I2C_EC.WAKE_UP */
                /* Wake up device from deep sleep on address match event. The matched address is NACKed */
                if(0u != (locIntrCause & EZI2C_INTR_CAUSE_I2C_EC))
                {
                    EZI2C_I2C_SLAVE_GENERATE_NACK; /* NACK in active mode */
                    EZI2C_ClearI2CExtClkInterruptSource(EZI2C_INTR_I2C_EC_WAKE_UP);
                }
            }
            #endif
        #endif /* (!EZI2C_CY_SCBIP_V0) */
        }

    #ifdef EZI2C_EZI2C_NO_STRETCH_ISR_EXIT_CALLBACK
        EZI2C_EZI2C_NO_STRETCH_ISR_ExitCallback();
    #endif /* EZI2C_EZI2C_NO_STRETCH_ISR_EXIT_CALLBACK */

    }
#endif /* (EZI2C_EZI2C_SCL_STRETCH_DISABLE_CONST) */


/* [] END OF FILE */
