cyrilknops/intelliflow/2020-2021/PCB/TestCodesPCB/PSoc_Slave_Codes/SPI_Slave_FullDuplex.cydsn/codegentemp/UART_Putty.c

/***************************************************************************//**
* \file UART_Putty.c
* \version 4.0
*
* \brief
*  This file provides the source code to the API for the SCB Component.
*
* Note:
*
*******************************************************************************
* \copyright
* Copyright 2013-2017, Cypress Semiconductor Corporation.  All rights reserved.
* You may use this file only in accordance with the license, terms, conditions,
* disclaimers, and limitations in the end user license agreement accompanying
* the software package with which this file was provided.
*******************************************************************************/

#include "UART_Putty_PVT.h"

#if (UART_Putty_SCB_MODE_I2C_INC)
    #include "UART_Putty_I2C_PVT.h"
#endif /* (UART_Putty_SCB_MODE_I2C_INC) */

#if (UART_Putty_SCB_MODE_EZI2C_INC)
    #include "UART_Putty_EZI2C_PVT.h"
#endif /* (UART_Putty_SCB_MODE_EZI2C_INC) */

#if (UART_Putty_SCB_MODE_SPI_INC || UART_Putty_SCB_MODE_UART_INC)
    #include "UART_Putty_SPI_UART_PVT.h"
#endif /* (UART_Putty_SCB_MODE_SPI_INC || UART_Putty_SCB_MODE_UART_INC) */


/***************************************
*    Run Time Configuration Vars
***************************************/

/* Stores internal component configuration for Unconfigured mode */
#if (UART_Putty_SCB_MODE_UNCONFIG_CONST_CFG)
    /* Common configuration variables */
    uint8 UART_Putty_scbMode = UART_Putty_SCB_MODE_UNCONFIG;
    uint8 UART_Putty_scbEnableWake;
    uint8 UART_Putty_scbEnableIntr;

    /* I2C configuration variables */
    uint8 UART_Putty_mode;
    uint8 UART_Putty_acceptAddr;

    /* SPI/UART configuration variables */
    volatile uint8 * UART_Putty_rxBuffer;
    uint8  UART_Putty_rxDataBits;
    uint32 UART_Putty_rxBufferSize;

    volatile uint8 * UART_Putty_txBuffer;
    uint8  UART_Putty_txDataBits;
    uint32 UART_Putty_txBufferSize;

    /* EZI2C configuration variables */
    uint8 UART_Putty_numberOfAddr;
    uint8 UART_Putty_subAddrSize;
#endif /* (UART_Putty_SCB_MODE_UNCONFIG_CONST_CFG) */


/***************************************
*     Common SCB Vars
***************************************/
/**
* \addtogroup group_general
* \{
*/

/** UART_Putty_initVar indicates whether the UART_Putty 
*  component has been initialized. The variable is initialized to 0 
*  and set to 1 the first time SCB_Start() is called. This allows 
*  the component to restart without reinitialization after the first 
*  call to the UART_Putty_Start() routine.
*
*  If re-initialization of the component is required, then the 
*  UART_Putty_Init() function can be called before the 
*  UART_Putty_Start() or UART_Putty_Enable() function.
*/
uint8 UART_Putty_initVar = 0u;


#if (! (UART_Putty_SCB_MODE_I2C_CONST_CFG || \
        UART_Putty_SCB_MODE_EZI2C_CONST_CFG))
    /** This global variable stores TX interrupt sources after 
    * UART_Putty_Stop() is called. Only these TX interrupt sources 
    * will be restored on a subsequent UART_Putty_Enable() call.
    */
    uint16 UART_Putty_IntrTxMask = 0u;
#endif /* (! (UART_Putty_SCB_MODE_I2C_CONST_CFG || \
              UART_Putty_SCB_MODE_EZI2C_CONST_CFG)) */
/** \} globals */

#if (UART_Putty_SCB_IRQ_INTERNAL)
#if !defined (CY_REMOVE_UART_Putty_CUSTOM_INTR_HANDLER)
    void (*UART_Putty_customIntrHandler)(void) = NULL;
#endif /* !defined (CY_REMOVE_UART_Putty_CUSTOM_INTR_HANDLER) */
#endif /* (UART_Putty_SCB_IRQ_INTERNAL) */


/***************************************
*    Private Function Prototypes
***************************************/

static void UART_Putty_ScbEnableIntr(void);
static void UART_Putty_ScbModeStop(void);
static void UART_Putty_ScbModePostEnable(void);


/*******************************************************************************
* Function Name: UART_Putty_Init
****************************************************************************//**
*
*  Initializes the UART_Putty component to operate in one of the selected
*  configurations: I2C, SPI, UART or EZI2C.
*  When the configuration is set to "Unconfigured SCB", this function does
*  not do any initialization. Use mode-specific initialization APIs instead:
*  UART_Putty_I2CInit, UART_Putty_SpiInit, 
*  UART_Putty_UartInit or UART_Putty_EzI2CInit.
*
*******************************************************************************/
void UART_Putty_Init(void)
{
#if (UART_Putty_SCB_MODE_UNCONFIG_CONST_CFG)
    if (UART_Putty_SCB_MODE_UNCONFIG_RUNTM_CFG)
    {
        UART_Putty_initVar = 0u;
    }
    else
    {
        /* Initialization was done before this function call */
    }

#elif (UART_Putty_SCB_MODE_I2C_CONST_CFG)
    UART_Putty_I2CInit();

#elif (UART_Putty_SCB_MODE_SPI_CONST_CFG)
    UART_Putty_SpiInit();

#elif (UART_Putty_SCB_MODE_UART_CONST_CFG)
    UART_Putty_UartInit();

#elif (UART_Putty_SCB_MODE_EZI2C_CONST_CFG)
    UART_Putty_EzI2CInit();

#endif /* (UART_Putty_SCB_MODE_UNCONFIG_CONST_CFG) */
}


/*******************************************************************************
* Function Name: UART_Putty_Enable
****************************************************************************//**
*
*  Enables UART_Putty component operation: activates the hardware and 
*  internal interrupt. It also restores TX interrupt sources disabled after the 
*  UART_Putty_Stop() function was called (note that level-triggered TX 
*  interrupt sources remain disabled to not cause code lock-up).
*  For I2C and EZI2C modes the interrupt is internal and mandatory for 
*  operation. For SPI and UART modes the interrupt can be configured as none, 
*  internal or external.
*  The UART_Putty configuration should be not changed when the component
*  is enabled. Any configuration changes should be made after disabling the 
*  component.
*  When configuration is set to “Unconfigured UART_Putty”, the component 
*  must first be initialized to operate in one of the following configurations: 
*  I2C, SPI, UART or EZ I2C, using the mode-specific initialization API. 
*  Otherwise this function does not enable the component.
*
*******************************************************************************/
void UART_Putty_Enable(void)
{
#if (UART_Putty_SCB_MODE_UNCONFIG_CONST_CFG)
    /* Enable SCB block, only if it is already configured */
    if (!UART_Putty_SCB_MODE_UNCONFIG_RUNTM_CFG)
    {
        UART_Putty_CTRL_REG |= UART_Putty_CTRL_ENABLED;

        UART_Putty_ScbEnableIntr();

        /* Call PostEnable function specific to current operation mode */
        UART_Putty_ScbModePostEnable();
    }
#else
    UART_Putty_CTRL_REG |= UART_Putty_CTRL_ENABLED;

    UART_Putty_ScbEnableIntr();

    /* Call PostEnable function specific to current operation mode */
    UART_Putty_ScbModePostEnable();
#endif /* (UART_Putty_SCB_MODE_UNCONFIG_CONST_CFG) */
}


/*******************************************************************************
* Function Name: UART_Putty_Start
****************************************************************************//**
*
*  Invokes UART_Putty_Init() and UART_Putty_Enable().
*  After this function call, the component is enabled and ready for operation.
*  When configuration is set to "Unconfigured SCB", the component must first be
*  initialized to operate in one of the following configurations: I2C, SPI, UART
*  or EZI2C. Otherwise this function does not enable the component.
*
* \globalvars
*  UART_Putty_initVar - used to check initial configuration, modified
*  on first function call.
*
*******************************************************************************/
void UART_Putty_Start(void)
{
    if (0u == UART_Putty_initVar)
    {
        UART_Putty_Init();
        UART_Putty_initVar = 1u; /* Component was initialized */
    }

    UART_Putty_Enable();
}


/*******************************************************************************
* Function Name: UART_Putty_Stop
****************************************************************************//**
*
*  Disables the UART_Putty component: disable the hardware and internal 
*  interrupt. It also disables all TX interrupt sources so as not to cause an 
*  unexpected interrupt trigger because after the component is enabled, the 
*  TX FIFO is empty.
*  Refer to the function UART_Putty_Enable() for the interrupt 
*  configuration details.
*  This function disables the SCB component without checking to see if 
*  communication is in progress. Before calling this function it may be 
*  necessary to check the status of communication to make sure communication 
*  is complete. If this is not done then communication could be stopped mid 
*  byte and corrupted data could result.
*
*******************************************************************************/
void UART_Putty_Stop(void)
{
#if (UART_Putty_SCB_IRQ_INTERNAL)
    UART_Putty_DisableInt();
#endif /* (UART_Putty_SCB_IRQ_INTERNAL) */

    /* Call Stop function specific to current operation mode */
    UART_Putty_ScbModeStop();

    /* Disable SCB IP */
    UART_Putty_CTRL_REG &= (uint32) ~UART_Putty_CTRL_ENABLED;

    /* Disable all TX interrupt sources so as not to cause an unexpected
    * interrupt trigger after the component will be enabled because the 
    * TX FIFO is empty.
    * For SCB IP v0, it is critical as it does not mask-out interrupt
    * sources when it is disabled. This can cause a code lock-up in the
    * interrupt handler because TX FIFO cannot be loaded after the block
    * is disabled.
    */
    UART_Putty_SetTxInterruptMode(UART_Putty_NO_INTR_SOURCES);

#if (UART_Putty_SCB_IRQ_INTERNAL)
    UART_Putty_ClearPendingInt();
#endif /* (UART_Putty_SCB_IRQ_INTERNAL) */
}


/*******************************************************************************
* Function Name: UART_Putty_SetRxFifoLevel
****************************************************************************//**
*
*  Sets level in the RX FIFO to generate a RX level interrupt.
*  When the RX FIFO has more entries than the RX FIFO level an RX level
*  interrupt request is generated.
*
*  \param level: Level in the RX FIFO to generate RX level interrupt.
*   The range of valid level values is between 0 and RX FIFO depth - 1.
*
*******************************************************************************/
void UART_Putty_SetRxFifoLevel(uint32 level)
{
    uint32 rxFifoCtrl;

    rxFifoCtrl = UART_Putty_RX_FIFO_CTRL_REG;

    rxFifoCtrl &= ((uint32) ~UART_Putty_RX_FIFO_CTRL_TRIGGER_LEVEL_MASK); /* Clear level mask bits */
    rxFifoCtrl |= ((uint32) (UART_Putty_RX_FIFO_CTRL_TRIGGER_LEVEL_MASK & level));

    UART_Putty_RX_FIFO_CTRL_REG = rxFifoCtrl;
}


/*******************************************************************************
* Function Name: UART_Putty_SetTxFifoLevel
****************************************************************************//**
*
*  Sets level in the TX FIFO to generate a TX level interrupt.
*  When the TX FIFO has less entries than the TX FIFO level an TX level
*  interrupt request is generated.
*
*  \param level: Level in the TX FIFO to generate TX level interrupt.
*   The range of valid level values is between 0 and TX FIFO depth - 1.
*
*******************************************************************************/
void UART_Putty_SetTxFifoLevel(uint32 level)
{
    uint32 txFifoCtrl;

    txFifoCtrl = UART_Putty_TX_FIFO_CTRL_REG;

    txFifoCtrl &= ((uint32) ~UART_Putty_TX_FIFO_CTRL_TRIGGER_LEVEL_MASK); /* Clear level mask bits */
    txFifoCtrl |= ((uint32) (UART_Putty_TX_FIFO_CTRL_TRIGGER_LEVEL_MASK & level));

    UART_Putty_TX_FIFO_CTRL_REG = txFifoCtrl;
}


#if (UART_Putty_SCB_IRQ_INTERNAL)
    /*******************************************************************************
    * Function Name: UART_Putty_SetCustomInterruptHandler
    ****************************************************************************//**
    *
    *  Registers a function to be called by the internal interrupt handler.
    *  First the function that is registered is called, then the internal interrupt
    *  handler performs any operation such as software buffer management functions
    *  before the interrupt returns.  It is the user's responsibility not to break
    *  the software buffer operations. Only one custom handler is supported, which
    *  is the function provided by the most recent call.
    *  At the initialization time no custom handler is registered.
    *
    *  \param func: Pointer to the function to register.
    *        The value NULL indicates to remove the current custom interrupt
    *        handler.
    *
    *******************************************************************************/
    void UART_Putty_SetCustomInterruptHandler(void (*func)(void))
    {
    #if !defined (CY_REMOVE_UART_Putty_CUSTOM_INTR_HANDLER)
        UART_Putty_customIntrHandler = func; /* Register interrupt handler */
    #else
        if (NULL != func)
        {
            /* Suppress compiler warning */
        }
    #endif /* !defined (CY_REMOVE_UART_Putty_CUSTOM_INTR_HANDLER) */
    }
#endif /* (UART_Putty_SCB_IRQ_INTERNAL) */


/*******************************************************************************
* Function Name: UART_Putty_ScbModeEnableIntr
****************************************************************************//**
*
*  Enables an interrupt for a specific mode.
*
*******************************************************************************/
static void UART_Putty_ScbEnableIntr(void)
{
#if (UART_Putty_SCB_IRQ_INTERNAL)
    /* Enable interrupt in NVIC */
    #if (UART_Putty_SCB_MODE_UNCONFIG_CONST_CFG)
        if (0u != UART_Putty_scbEnableIntr)
        {
            UART_Putty_EnableInt();
        }

    #else
        UART_Putty_EnableInt();

    #endif /* (UART_Putty_SCB_MODE_UNCONFIG_CONST_CFG) */
#endif /* (UART_Putty_SCB_IRQ_INTERNAL) */
}


/*******************************************************************************
* Function Name: UART_Putty_ScbModePostEnable
****************************************************************************//**
*
*  Calls the PostEnable function for a specific operation mode.
*
*******************************************************************************/
static void UART_Putty_ScbModePostEnable(void)
{
#if (UART_Putty_SCB_MODE_UNCONFIG_CONST_CFG)
#if (!UART_Putty_CY_SCBIP_V1)
    if (UART_Putty_SCB_MODE_SPI_RUNTM_CFG)
    {
        UART_Putty_SpiPostEnable();
    }
    else if (UART_Putty_SCB_MODE_UART_RUNTM_CFG)
    {
        UART_Putty_UartPostEnable();
    }
    else
    {
        /* Unknown mode: do nothing */
    }
#endif /* (!UART_Putty_CY_SCBIP_V1) */

#elif (UART_Putty_SCB_MODE_SPI_CONST_CFG)
    UART_Putty_SpiPostEnable();

#elif (UART_Putty_SCB_MODE_UART_CONST_CFG)
    UART_Putty_UartPostEnable();

#else
    /* Unknown mode: do nothing */
#endif /* (UART_Putty_SCB_MODE_UNCONFIG_CONST_CFG) */
}


/*******************************************************************************
* Function Name: UART_Putty_ScbModeStop
****************************************************************************//**
*
*  Calls the Stop function for a specific operation mode.
*
*******************************************************************************/
static void UART_Putty_ScbModeStop(void)
{
#if (UART_Putty_SCB_MODE_UNCONFIG_CONST_CFG)
    if (UART_Putty_SCB_MODE_I2C_RUNTM_CFG)
    {
        UART_Putty_I2CStop();
    }
    else if (UART_Putty_SCB_MODE_EZI2C_RUNTM_CFG)
    {
        UART_Putty_EzI2CStop();
    }
#if (!UART_Putty_CY_SCBIP_V1)
    else if (UART_Putty_SCB_MODE_SPI_RUNTM_CFG)
    {
        UART_Putty_SpiStop();
    }
    else if (UART_Putty_SCB_MODE_UART_RUNTM_CFG)
    {
        UART_Putty_UartStop();
    }
#endif /* (!UART_Putty_CY_SCBIP_V1) */
    else
    {
        /* Unknown mode: do nothing */
    }
#elif (UART_Putty_SCB_MODE_I2C_CONST_CFG)
    UART_Putty_I2CStop();

#elif (UART_Putty_SCB_MODE_EZI2C_CONST_CFG)
    UART_Putty_EzI2CStop();

#elif (UART_Putty_SCB_MODE_SPI_CONST_CFG)
    UART_Putty_SpiStop();

#elif (UART_Putty_SCB_MODE_UART_CONST_CFG)
    UART_Putty_UartStop();

#else
    /* Unknown mode: do nothing */
#endif /* (UART_Putty_SCB_MODE_UNCONFIG_CONST_CFG) */
}
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
