cyrilknops/intelliflow/2020-2021/PCB/TestCodesPCB/PSoc_Slave_Codes/SPI_Slave_FullDuplex.cydsn/codegentemp/UART_Putty_SPI_UART.c

/***************************************************************************//**
* \file UART_Putty_SPI_UART.c
* \version 4.0
*
* \brief
*  This file provides the source code to the API for the SCB Component in
*  SPI and UART modes.
*
* Note:
*
*******************************************************************************
* \copyright
* Copyright 2013-2017, Cypress Semiconductor Corporation.  All rights reserved.
* You may use this file only in accordance with the license, terms, conditions,
* disclaimers, and limitations in the end user license agreement accompanying
* the software package with which this file was provided.
*******************************************************************************/

#include "UART_Putty_PVT.h"
#include "UART_Putty_SPI_UART_PVT.h"

/***************************************
*        SPI/UART Private Vars
***************************************/

#if(UART_Putty_INTERNAL_RX_SW_BUFFER_CONST)
    /* Start index to put data into the software receive buffer.*/
    volatile uint32 UART_Putty_rxBufferHead;
    /* Start index to get data from the software receive buffer.*/
    volatile uint32 UART_Putty_rxBufferTail;
    /**
    * \addtogroup group_globals
    * \{
    */
    /** Sets when internal software receive buffer overflow
    *  was occurred.
    */
    volatile uint8  UART_Putty_rxBufferOverflow;
    /** \} globals */
#endif /* (UART_Putty_INTERNAL_RX_SW_BUFFER_CONST) */

#if(UART_Putty_INTERNAL_TX_SW_BUFFER_CONST)
    /* Start index to put data into the software transmit buffer.*/
    volatile uint32 UART_Putty_txBufferHead;
    /* Start index to get data from the software transmit buffer.*/
    volatile uint32 UART_Putty_txBufferTail;
#endif /* (UART_Putty_INTERNAL_TX_SW_BUFFER_CONST) */

#if(UART_Putty_INTERNAL_RX_SW_BUFFER)
    /* Add one element to the buffer to receive full packet. One byte in receive buffer is always empty */
    volatile uint8 UART_Putty_rxBufferInternal[UART_Putty_INTERNAL_RX_BUFFER_SIZE];
#endif /* (UART_Putty_INTERNAL_RX_SW_BUFFER) */
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
